95lux/aware01/firmware/Core/Inc/main.h

#define V_OCT_IN_Pin GPIO_PIN_0
#define V_OCT_IN_GPIO_Port GPIOC
#define CV1_IN_Pin GPIO_PIN_1
#define CV1_IN_GPIO_Port GPIOC
#define CV2_IN_Pin GPIO_PIN_2
#define CV2_IN_GPIO_Port GPIOC
#define CV3_IN_Pin GPIO_PIN_3
#define CV3_IN_GPIO_Port GPIOC
#define FADER1_IN_Pin GPIO_PIN_7
#define FADER1_IN_GPIO_Port GPIOA
#define FADER2_IN_Pin GPIO_PIN_5
#define FADER2_IN_GPIO_Port GPIOC
#define FADER3_IN_Pin GPIO_PIN_0
#define FADER3_IN_GPIO_Port GPIOB
#define FADER4_IN_Pin GPIO_PIN_1
#define FADER4_IN_GPIO_Port GPIOB
#define FAD_LED4_OUT_Pin GPIO_PIN_12
#define FAD_LED4_OUT_GPIO_Port GPIOB
#define FAD_LED3_OUT_Pin GPIO_PIN_13
#define FAD_LED3_OUT_GPIO_Port GPIOB
#define FAD_LED2_OUT_Pin GPIO_PIN_14
#define FAD_LED2_OUT_GPIO_Port GPIOB
#define FAD_LED1_OUT_Pin GPIO_PIN_15
#define FAD_LED1_OUT_GPIO_Port GPIOB
#define GATE3_IN_Pin GPIO_PIN_6
#define GATE3_IN_GPIO_Port GPIOC
#define GATE3_IN_EXTI_IRQn EXTI9_5_IRQn
#define GATE4_IN_Pin GPIO_PIN_7
#define GATE4_IN_GPIO_Port GPIOC
#define GATE4_IN_EXTI_IRQn EXTI9_5_IRQn
#define GATE2_IN_Pin GPIO_PIN_8
#define GATE2_IN_GPIO_Port GPIOA
#define GATE2_IN_EXTI_IRQn EXTI9_5_IRQn
#define GATE1_IN_Pin GPIO_PIN_9
#define GATE1_IN_GPIO_Port GPIOA
#define GATE1_IN_EXTI_IRQn EXTI9_5_IRQn
#define BUTTON1_IN_Pin GPIO_PIN_10
#define BUTTON1_IN_GPIO_Port GPIOA
#define BUTTON1_IN_EXTI_IRQn EXTI15_10_IRQn
#define BUTTON2_IN_Pin GPIO_PIN_11
#define BUTTON2_IN_GPIO_Port GPIOA
#define BUTTON2_IN_EXTI_IRQn EXTI15_10_IRQn
#define RGB_LED_DATA_Pin GPIO_PIN_12
#define RGB_LED_DATA_GPIO_Port GPIOC
