95lux/aware01/firmware/Aware/Inc/drivers/ws2812_driver.h

/**
 * @file ws2812_driver.h
 * @brief WS2812B RGB LED driver with animation state machine.
 */
#pragma once

#include "FreeRTOS.h"
#include "stdbool.h"
#include "stdint.h"
#include "stm32h7xx_hal.h"
#include "string.h"
#include "task.h"
#include "tim.h"
#include <stdint.h>

#define WS2812_LED_COUNT 4         // number of LEDs on the device
#define WS2812_ANIM_STAGE_COUNT 16 // maximum number of stages per animation, can be extended if needed

typedef struct {
    TIM_HandleTypeDef* htim_anim;
    TIM_HandleTypeDef* htim_pwm;
    uint32_t tim_channel_pwm;
    struct led_animation* default_animation;
    TaskHandle_t userIfTaskHandle;
} ws2812_init_t;

struct ws2812_color {
    uint8_t r;
    uint8_t g;
    uint8_t b;
};

struct led_animation_stage {
    uint32_t duration;
    struct ws2812_color leds[WS2812_LED_COUNT];
};

struct led_animation {
    struct led_animation_stage stages[WS2812_ANIM_STAGE_COUNT];
    uint32_t total_stages;
    uint32_t duration;
    bool running;
};

typedef enum { WS2812_MODE_OFF = 0, WS2812_MODE_STATIC, WS2812_MODE_TRIGGER, WS2812_MODE_ANIMATION } ws2812_mode_t;

/* ===== API ===== */
void ws2812_init(const ws2812_init_t* init_cfg);
void ws2812_start();

void ws2812_trigger_led(uint32_t idx, struct ws2812_color color, uint32_t timeout_ticks);
/* ===== Animation control ===== */

void ws2812_change_animation(uint32_t indx, struct led_animation* anim);
void ws2812_change_animation_all(struct led_animation* anim);
void ws2812_stop_animation(void);
void ws2812_run_step(void);
void ws2812_set_static_color(uint32_t idx, struct ws2812_color color);

/* ===== Timer hook (called from HAL_TIM_PeriodElapsedCallback) ===== */
void ws2812_timer_callback(TIM_HandleTypeDef* htim);
