95lux/aware01/firmware/Aware/Inc/tape_player.h

/**
 * @file tape_player.h
 * @brief Tape sampler: buffer structures, FSM events, and audio processing API.
 */
#pragma once

#include "audioengine.h"
#include "envelope.h"
#include "param_cache.h"
#include "project_config.h"

#include <stdbool.h>
#include <stddef.h>
#include <stdint.h>

#define MAX_NUM_SLICES 128

typedef struct {
    int16_t* ch[2];         // ch[0]=L, ch[1]=R
    uint32_t size;          // samples per channel
    uint32_t valid_samples; // number of valid recorded samples in the buffer (for playback), updated when recording is done
    uint8_t decimation;     // decimation factor for recording and playback

    uint32_t slice_positions[MAX_NUM_SLICES]; // holds start position of each slice in samples.
    uint32_t num_slices;
} tape_buffer_t;

// holds changeable parameters in the tape player engine. should actually not be accessed from outside
struct parameters {
    float pitch_factor;
    float starting_position; // currently not used
    float env_attack;
    float env_decay;

    // playback modes
    bool reverse;
    bool cyclic_mode;

    uint8_t decimation; // decimation factor for recording and playback.

    // normalized slice position, set from CV. This is used to calculate the actual slice start position in samples when starting playback or retriggering.
    float slice_pos;

    float grit; // calculated from decimation factor, used for excite effect amount in audio processing task. 0..1 depending on decimation.
};

// FSM logic
typedef enum { TAPE_EVT_NONE = 0, TAPE_EVT_PLAY, TAPE_EVT_STOP, TAPE_EVT_RECORD, TAPE_EVT_RECORD_DONE, TAPE_EVT_SWAP_DONE } tape_event_t;

typedef enum { PLAY_STOPPED = 0, PLAY_PLAYING } play_state_t;

typedef enum { REC_IDLE = 0, REC_RECORDING, REC_REREC, REC_DONE } rec_state_t;

typedef struct {
    bool active;
    uint32_t len;
    bool
        crossfade; // if crossfade is enabled, we are using temp_buf. Otherwise this struct just holds the position and length for simple in/out fades.

    // tracking the second playhead for crossfade
    uint64_t pos_q48_16; // 48.16 fixed point: upper 48 bits are integer index, lower 16 bits are fractional part

    // 16.16 fixed point fade accumulator for fade curve interpolation, independent of main playhead position and increment, so that we can have smooth fades even with low pitch factors (where main playhead moves very slowly and thus would cause stepping in the fade curve)
    // this is just the phase accumulator for the lut access.
    uint32_t fade_acc_q16;
    uint32_t step_q16; // how much to increment the fade_acc every sample, in Q16.16 format. Calculated from fade length and LUT size.
    uint32_t
        base_ratio_q16; // for crossfades, this is the ratio between the xfade buffer and the fade LUT, in Q16.16 format. Calculated from xfade length and LUT size.

    int16_t* buf_b_ptr_l;
    int16_t* buf_b_ptr_r;
    uint32_t
        temp_buf_valid_samples; // number of valid samples in the xfade temp buffer (for retrigger xfade at end of recording, when there might be less than xfade.len samples available)

} crossfade_t;

// main tape player structure
struct tape_player {
    size_t dma_buf_size;         // buffer size RX/TX
    tape_buffer_t* playback_buf; // pointer to the tape buffer that is currently used for playback.
    tape_buffer_t* record_buf;   // pointer to the tape buffer that is currently used for recording.
                                 // target of the tape

    uint64_t pos_q48_16; // main playhead position in Q48.16 format. Fractional part is 16bits for performance reasons

    bool cyclic_mode;

    crossfade_t xfade_retrig; // crossfade that is used on retrigger sample playback.
    crossfade_t xfade_cyclic; // crossfade that is used on cyclic playback mode.
    crossfade_t fade_in;      // simple fade in when starting playback
    crossfade_t fade_out;     // simple fadeout when approaching end of playback buffer

    uint32_t tape_recordhead;

    bool swap_bufs_pending;
    bool switch_bufs_done;

    uint32_t curr_phase_inc_q16_16; // The increment actually being used

    // states
    play_state_t play_state;
    rec_state_t rec_state;

    envelope_t env;

    struct parameters params;
};

// FREERTOS queue message structure
typedef enum { TAPE_CMD_PLAY, TAPE_CMD_STOP, TAPE_CMD_RECORD, TAPE_CMD_SLICE } tape_cmd_t;
typedef struct {
    tape_cmd_t cmd;
} tape_cmd_msg_t;

// Public API
int init_tape_player(size_t dma_buf_size);

// entry point for tape player audio processing. The whole implementation is inside tape_player_dsp.c
void tape_player_process(int16_t* in_buf, int16_t* out_buf);

void tape_player_play();
void tape_player_stop_play();
void tape_player_record();
void tape_player_stop_record(void);
void tape_player_set_params(struct param_cache param_cache);
void tape_player_set_slice();

float tape_player_get_grit();
float tape_player_get_pitch();
