95lux/aware01/firmware/Aware/Src/param_cache.c

/**
 * @file param_cache.c
 * @brief Parameter cache setters/getters for multi-source parameter sharing.
 */
#include "param_cache.h"

#include "FreeRTOS.h"
#include "atomic.h"
#include "task.h"

static volatile struct param_cache cache;

/* ===== Writers ===== */
void param_cache_set_pitch_cv(float v) {
    cache.pitch_cv = v;
}

void param_cache_set_pitch_ui(float v) {
    cache.pitch_ui = v;
}

void param_cache_set_env_attack(float attack) {
    cache.env_attack = attack;
}

void param_cache_set_env_decay(float decay) {
    cache.env_decay = decay;
}

void param_cache_set_cyclic(bool cyclic) {
    cache.cyclic_mode = cyclic;
}

void param_cache_set_reverse(bool reverse) {
    cache.reverse_mode = reverse;
}

void param_cache_set_decimation(uint8_t decimation) {
    cache.decimation = decimation;
}

void param_cache_set_slice_pos(float slice_pos) {
    cache.slice_pos = slice_pos;
}

void param_cache_set_xy_fx(float val_x, float val_y) {
    cache.fx_x = val_x;
    cache.fx_y = val_y;
}

void param_cache_set_schroeder_verb_size(float size) {
    cache.schroeder_verb_size = size;
}
void param_cache_set_schroeder_verb_feedback(float feedback) {
    cache.schroeder_verb_feedback = feedback;
}
void param_cache_set_schroeder_verb_wet(float wet) {
    cache.schroeder_verb_wet = wet;
}

void param_cache_set_schroeder_verb_lp_alpha(float alpha) {
    cache.schroeder_verb_lp_alpha = alpha;
}

/* ===== Reader ===== */
void param_cache_fetch(struct param_cache* out) {
    out->pitch_cv = cache.pitch_cv;
    out->pitch_ui = cache.pitch_ui;
    out->env_attack = cache.env_attack;
    out->env_decay = cache.env_decay;
    out->cyclic_mode = cache.cyclic_mode;
    out->reverse_mode = cache.reverse_mode;
    out->decimation = cache.decimation;
    out->slice_pos = cache.slice_pos;
    out->fx_x = cache.fx_x;
    out->fx_y = cache.fx_y;
    out->schroeder_verb_size = cache.schroeder_verb_size;
    out->schroeder_verb_feedback = cache.schroeder_verb_feedback;
    out->schroeder_verb_wet = cache.schroeder_verb_wet;
    out->schroeder_verb_lp_alpha = cache.schroeder_verb_lp_alpha;
}
