95lux/aware01/firmware/Aware/Inc/audioengine.h

/**
 * @file audioengine.h
 * @brief I2S DMA audio engine: init, start, and buffer I/O.
 */
#pragma once

#include "FreeRTOS.h"
#include "i2s.h"
#include "project_config.h"
#include "semphr.h"
#include <math.h>
#include <stdbool.h>
#include <stdint.h>
#include <sys/_intsup.h>

// return types
#define AUDIOENGINE_OK 0
#define AUDIOENGINE_ERROR -1
#define AUDIOENGINE_NOT_INITIALIZED -2

struct audioengine_config {
    I2S_HandleTypeDef* i2s_handle;
    uint32_t sample_rate;
    uint16_t buffer_size;

    TaskHandle_t audioTaskHandle;
    volatile int16_t* tx_buf_ptr;
    volatile int16_t* rx_buf_ptr;
};

int init_audioengine(struct audioengine_config* config);
int start_audio_engine(void);

void audio_get_dma_in_buf(int16_t* buf, uint32_t buf_size);
void audio_write_dma_out_buf(int16_t* buf, uint32_t buf_size);

// Test Functions
void generateSineWave(uint16_t* phaseIndex, double phaseIncrement);
void receiveTest();
void initSineTable();

void loopback_samples();
