95lux/aware01/firmware/Aware/Inc/param_cache.h

/**
 * @file param_cache.h
 * @brief Thread-safe parameter snapshot shared between UI/CV and audio tasks.
 */
#pragma once
#include <stdbool.h>
#include <stdint.h>

// Shared memory structure for parameters that are set from multiple sources (UI, CV) and need to be accessed in the audio processing code.

struct param_cache {
    float pitch_cv;
    float pitch_ui;
    float env_attack;
    float env_decay;

    bool cyclic_mode;
    bool reverse_mode;

    uint8_t decimation;

    float slice_pos; // normalized slice position

    float fx_x;
    float fx_y;

    float schroeder_verb_size;
    float schroeder_verb_feedback;
    float schroeder_verb_wet;
    float schroeder_verb_lp_alpha;
};

/* public API */
void param_cache_set_pitch_cv(float v);
void param_cache_set_pitch_ui(float v);
void param_cache_set_env_attack(float attack);
void param_cache_set_env_decay(float decay);
void param_cache_set_cyclic(bool cyclic);
void param_cache_set_reverse(bool reverse);
void param_cache_set_decimation(uint8_t decimation);
void param_cache_set_slice_pos(float slice_pos);
void param_cache_set_xy_fx(float x, float y);
void param_cache_set_schroeder_verb_size(float size);
void param_cache_set_schroeder_verb_feedback(float feedback);
void param_cache_set_schroeder_verb_wet(float wet);
void param_cache_set_schroeder_verb_lp_alpha(float cutoff);

void param_cache_fetch(struct param_cache* out);
