95lux/aware01/firmware/Aware/Inc/ressources.h

/**
 * @file ressources.h
 * @brief Pre-computed LUTs and IIR filter coefficients.
 */
#include "arm_math.h"

#include "project_config.h"

#define FADE_LUT_LEN 256
extern int16_t fade_in_lut[FADE_LUT_LEN];

// Coefficients for IIR filter in CMSIS-DSP format (b0, b1, b2, -a1, -a2)

#define BIQUAD_CASCADE_NUM_STAGES 3
extern float32_t iir_coeffs[BIQUAD_CASCADE_NUM_STAGES * 5];

#define lp_fc2k_but_NUM_STAGES 1
extern float32_t lp_fc2k_but_coeffs[lp_fc2k_but_NUM_STAGES * 5];
