95lux/aware01/firmware/Aware/Src/ressources.c

/**
 * @file ressources.c
 * @brief LUT data: fade-in curve, IIR coefficients, and Butterworth lowpass coefficients.
 */
#include "ressources.h"

int16_t fade_in_lut[FADE_LUT_LEN] = {
    0,     202,   404,   605,   807,   1009,  1211,  1412,  1614,  1816,  2017,  2219,  2420,  2621,  2822,  3023,  3224,  3425,  3626,
    3826,  4027,  4227,  4427,  4627,  4827,  5026,  5226,  5425,  5624,  5822,  6021,  6219,  6417,  6615,  6813,  7010,  7207,  7404,
    7600,  7796,  7992,  8188,  8383,  8578,  8773,  8967,  9161,  9355,  9548,  9741,  9933,  10126, 10317, 10509, 10700, 10890, 11080,
    11270, 11459, 11648, 11837, 12025, 12212, 12399, 12586, 12772, 12958, 13143, 13328, 13512, 13695, 13878, 14061, 14243, 14425, 14606,
    14786, 14966, 15145, 15324, 15502, 15679, 15856, 16033, 16208, 16383, 16558, 16732, 16905, 17078, 17250, 17421, 17592, 17761, 17931,
    18099, 18267, 18434, 18601, 18767, 18932, 19096, 19260, 19423, 19585, 19747, 19907, 20067, 20226, 20385, 20542, 20699, 20855, 21011,
    21165, 21319, 21472, 21624, 21775, 21925, 22075, 22224, 22372, 22519, 22665, 22810, 22955, 23098, 23241, 23383, 23524, 23664, 23803,
    23941, 24079, 24215, 24351, 24485, 24619, 24752, 24883, 25014, 25144, 25273, 25401, 25528, 25654, 25779, 25903, 26026, 26149, 26270,
    26390, 26509, 26627, 26744, 26860, 26976, 27090, 27203, 27315, 27426, 27536, 27644, 27752, 27859, 27965, 28069, 28173, 28276, 28377,
    28477, 28577, 28675, 28772, 28868, 28963, 29057, 29150, 29241, 29332, 29421, 29510, 29597, 29683, 29768, 29851, 29934, 30016, 30096,
    30175, 30253, 30330, 30406, 30481, 30554, 30627, 30698, 30768, 30837, 30904, 30971, 31036, 31100, 31163, 31225, 31286, 31345, 31403,
    31460, 31516, 31571, 31624, 31676, 31728, 31777, 31826, 31873, 31920, 31965, 32008, 32051, 32092, 32132, 32171, 32209, 32246, 32281,
    32315, 32348, 32379, 32410, 32439, 32467, 32493, 32519, 32543, 32566, 32587, 32608, 32627, 32645, 32662, 32678, 32692, 32705, 32717,
    32727, 32737, 32745, 32751, 32757, 32761, 32765, 32766, 32767,
};

float32_t iir_coeffs[BIQUAD_CASCADE_NUM_STAGES * 5] = {
    0.46538463,
    -0.93384347,
    0.46846562,
    1.34907999,
    -0.46023366,
    1.00000000,
    -1.99341221,
    0.99342666,
    1.45424359,
    -0.57406192,
    1.00000000,
    -1.99998205,
    0.99999656,
    1.68123943,
    -0.81976044,
};

float32_t lp_fc2k_but_coeffs[lp_fc2k_but_NUM_STAGES * 5] = {
    0.01440144,
    0.02880288,
    0.01440144,
    1.63299316,
    -0.69059892,
};
